lixtheyt/mediapad/PCB/Hackpad.kicad_sch

## KiCad design PCB/Hackpad.kicad_sch (2026-07-23)

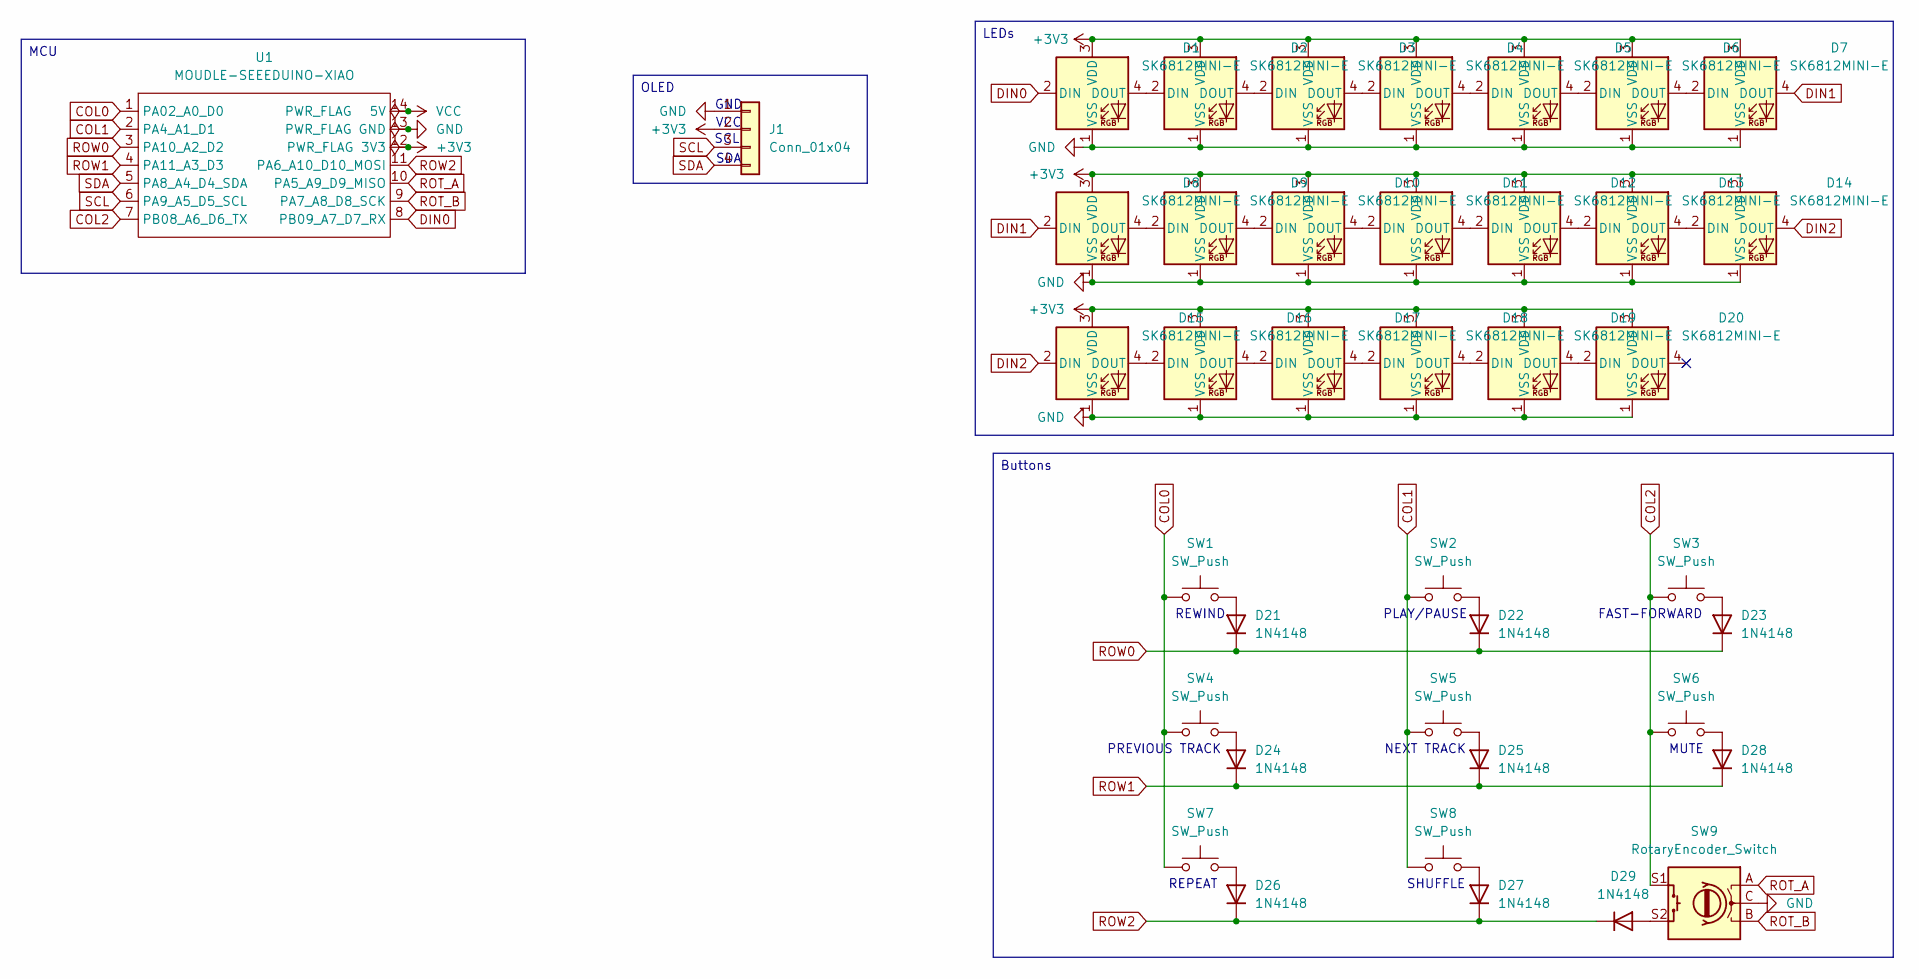
[picture p8: schematic Hackpad.kicad_sch]

Parts:
D1, D2, D3, D4, D5, D6, D7, D8, D9, D10, D11, D12, D13, D14, D15, D16, D17, D18, D19, D20: SK6812MINI-E; SK6812MINI-E_fixed
D21, D22, D23, D24, D25, D26, D27, D28, D29: 1N4148; D_DO-35_SOD27_P7.62mm_Horizontal
J1: Conn_01x04; SSD1306-0.91-OLED-4pin-128x32
SW1, SW2, SW3, SW4, SW5, SW6, SW7, SW8: SW_Push; SW_Cherry_MX_1.00u_PCB
SW9: RotaryEncoder_Switch; RotaryEncoder_Alps_EC11E-Switch_Vertical_H20mm
U1: MOUDLE-SEEEDUINO-XIAO; XIAO-Generic-Hybrid-14P-2.54-21X17.8MM

Connections:
+3V3: D1.3 (VDD), D2.3 (VDD), D3.3 (VDD), D4.3 (VDD), D5.3 (VDD), D6.3 (VDD), D7.3 (VDD), D8.3 (VDD), D9.3 (VDD), D10.3 (VDD), D11.3 (VDD), D12.3 (VDD), D13.3 (VDD), D14.3 (VDD), D15.3 (VDD), D16.3 (VDD), D17.3 (VDD), D18.3 (VDD), D19.3 (VDD), D20.3 (VDD), J1.2, U1.12 (3V3)
COL0: SW1.1, SW4.1, SW7.1, U1.1 (PA02_A0_D0)
COL1: SW2.1, SW5.1, SW8.1, U1.2 (PA4_A1_D1)
COL2: SW3.1, SW6.1, SW9.S1, U1.7 (PB08_A6_D6_TX)
DIN0: D1.2 (DIN), U1.8 (PB09_A7_D7_RX)
DIN1: D7.4 (DOUT), D8.2 (DIN)
DIN2: D14.4 (DOUT), D15.2 (DIN)
GND: D1.1 (VSS), D2.1 (VSS), D3.1 (VSS), D4.1 (VSS), D5.1 (VSS), D6.1 (VSS), D7.1 (VSS), D8.1 (VSS), D9.1 (VSS), D10.1 (VSS), D11.1 (VSS), D12.1 (VSS), D13.1 (VSS), D14.1 (VSS), D15.1 (VSS), D16.1 (VSS), D17.1 (VSS), D18.1 (VSS), D19.1 (VSS), D20.1 (VSS), J1.1, SW9.C, U1.13 (GND)
unnamed: D1.4 (DOUT), D2.2 (DIN)
unnamed: D2.4 (DOUT), D3.2 (DIN)
unnamed: D3.4 (DOUT), D4.2 (DIN)
unnamed: D4.4 (DOUT), D5.2 (DIN)
unnamed: D5.4 (DOUT), D6.2 (DIN)
unnamed: D6.4 (DOUT), D7.2 (DIN)
unnamed: D8.4 (DOUT), D9.2 (DIN)
unnamed: D9.4 (DOUT), D10.2 (DIN)
unnamed: D10.4 (DOUT), D11.2 (DIN)
unnamed: D11.4 (DOUT), D12.2 (DIN)
unnamed: D12.4 (DOUT), D13.2 (DIN)
unnamed: D13.4 (DOUT), D14.2 (DIN)
unnamed: D15.4 (DOUT), D16.2 (DIN)
unnamed: D16.4 (DOUT), D17.2 (DIN)
unnamed: D17.4 (DOUT), D18.2 (DIN)
unnamed: D18.4 (DOUT), D19.2 (DIN)
unnamed: D19.4 (DOUT), D20.2 (DIN)
unnamed: D21.2 (A), SW1.2
unnamed: D22.2 (A), SW2.2
unnamed: D23.2 (A), SW3.2
unnamed: D24.2 (A), SW4.2
unnamed: D25.2 (A), SW5.2
unnamed: D26.2 (A), SW7.2
unnamed: D27.2 (A), SW8.2
unnamed: D28.2 (A), SW6.2
unnamed: D29.2 (A), SW9.S2
ROT_A: SW9.A, U1.10 (PA5_A9_D9_MISO)
ROT_B: SW9.B, U1.9 (PA7_A8_D8_SCK)
ROW0: D21.1 (K), D22.1 (K), D23.1 (K), U1.3 (PA10_A2_D2)
ROW1: D24.1 (K), D25.1 (K), D28.1 (K), U1.4 (PA11_A3_D3)
ROW2: D26.1 (K), D27.1 (K), D29.1 (K), U1.11 (PA6_A10_D10_MOSI)
SCL: J1.3, U1.6 (PA9_A5_D5_SCL)
SDA: J1.4, U1.5 (PA8_A4_D4_SDA)
VCC: U1.14 (5V)

Notes on the sheet:
SDA
PLAY/PAUSE
PREVIOUS TRACK
REPEAT
VCC
SHUFFLE
GND
REWIND
SCL
MUTE
FAST-FORWARD
NEXT TRACK
OLED
LEDs
Buttons
MCU
